denilnicolosi/Rover_IoT/Raspberry/print_serial_port.py

import serial
import serial.tools.list_ports

#print serial port available
ports = serial.tools.list_ports.comports()
for port, desc, hwid in sorted(ports):
        print("{}: {} [{}]".format(port, desc, hwid))
